jrzwee/PiezoPiano/hardware/pinout/hardware.png

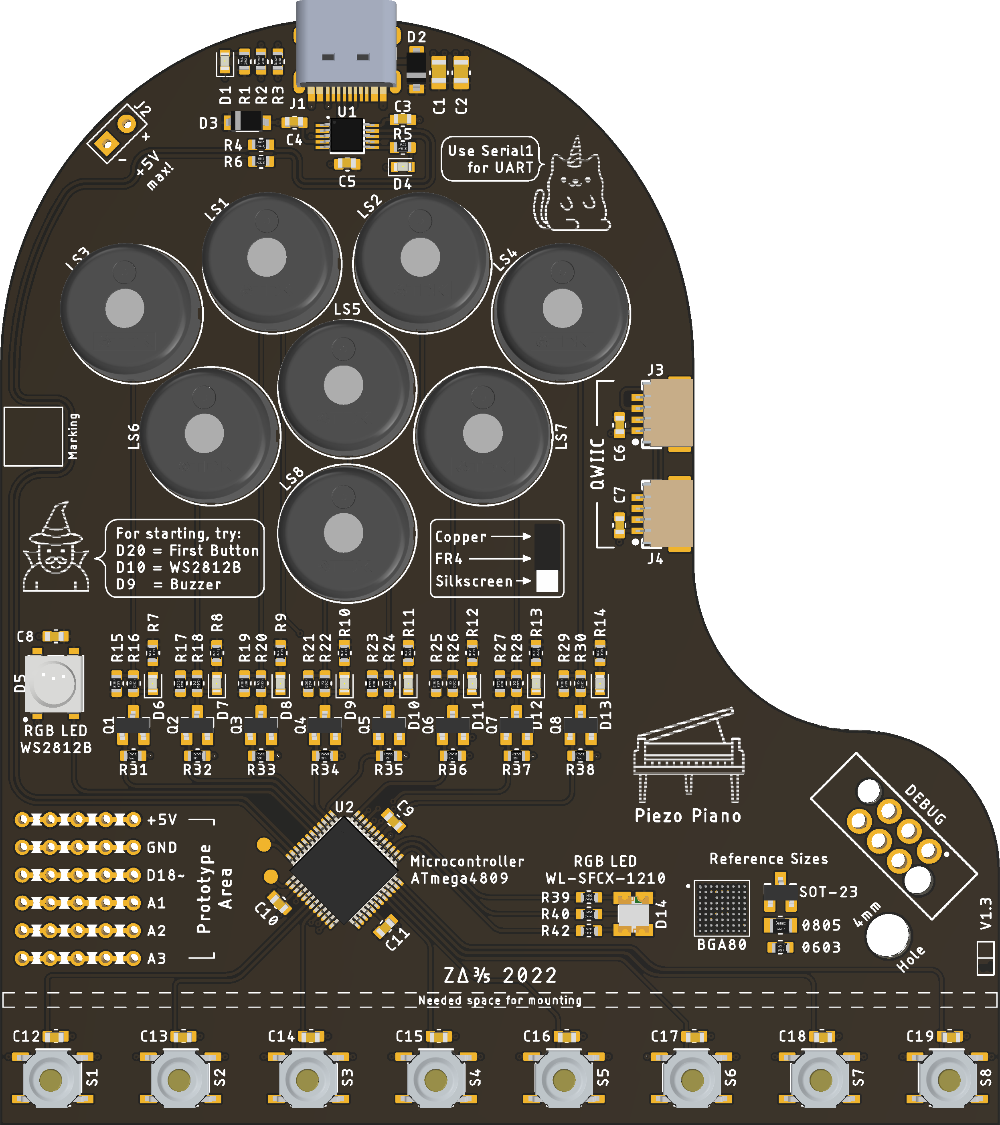
hardware/pinout/hardware.png
