jrzwee/PiezoPiano/hardware/renders/20211024_PiezoPiano_B_V1.2.png

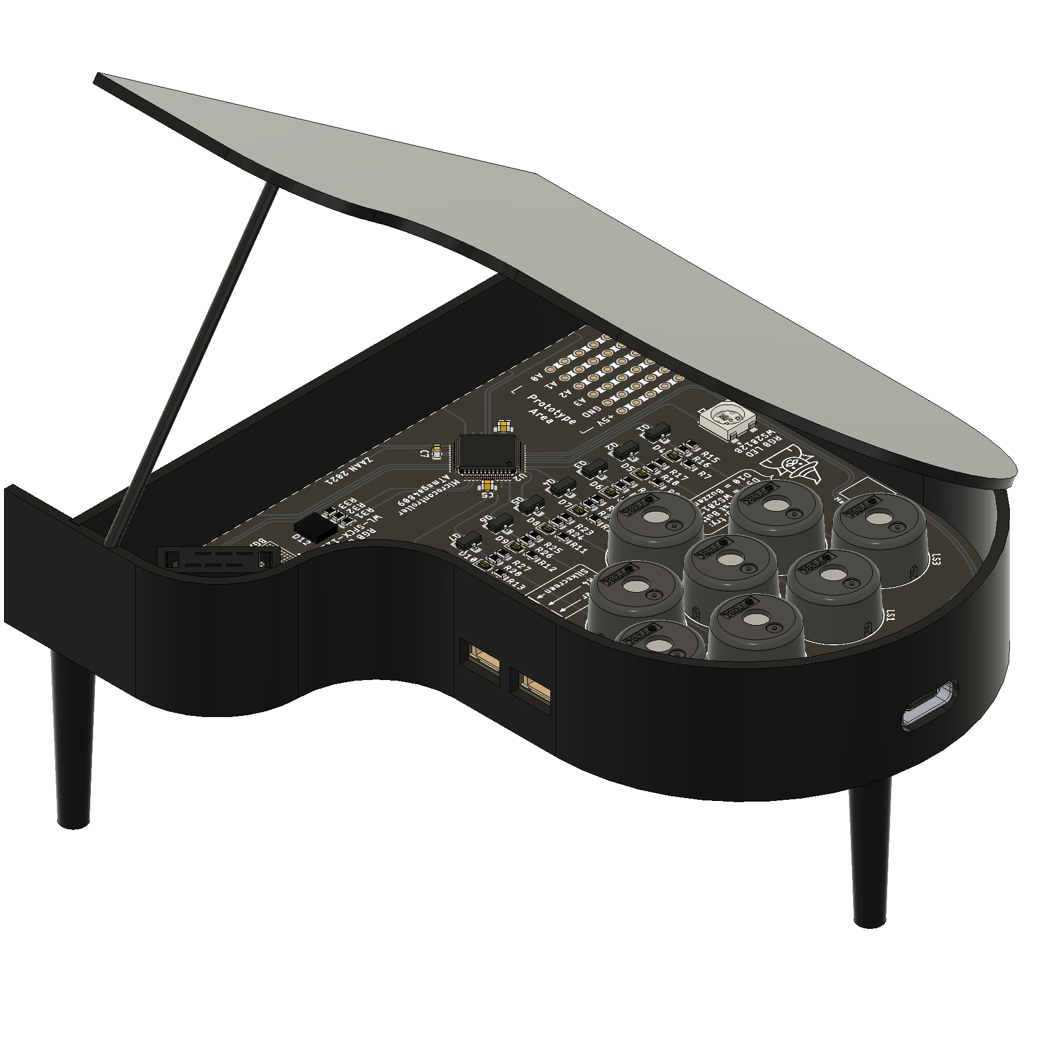
hardware/renders/20211024_PiezoPiano_B_V1.2.png
