jrzwee/PiezoPiano/hardware/renders/piezopiano_b.png

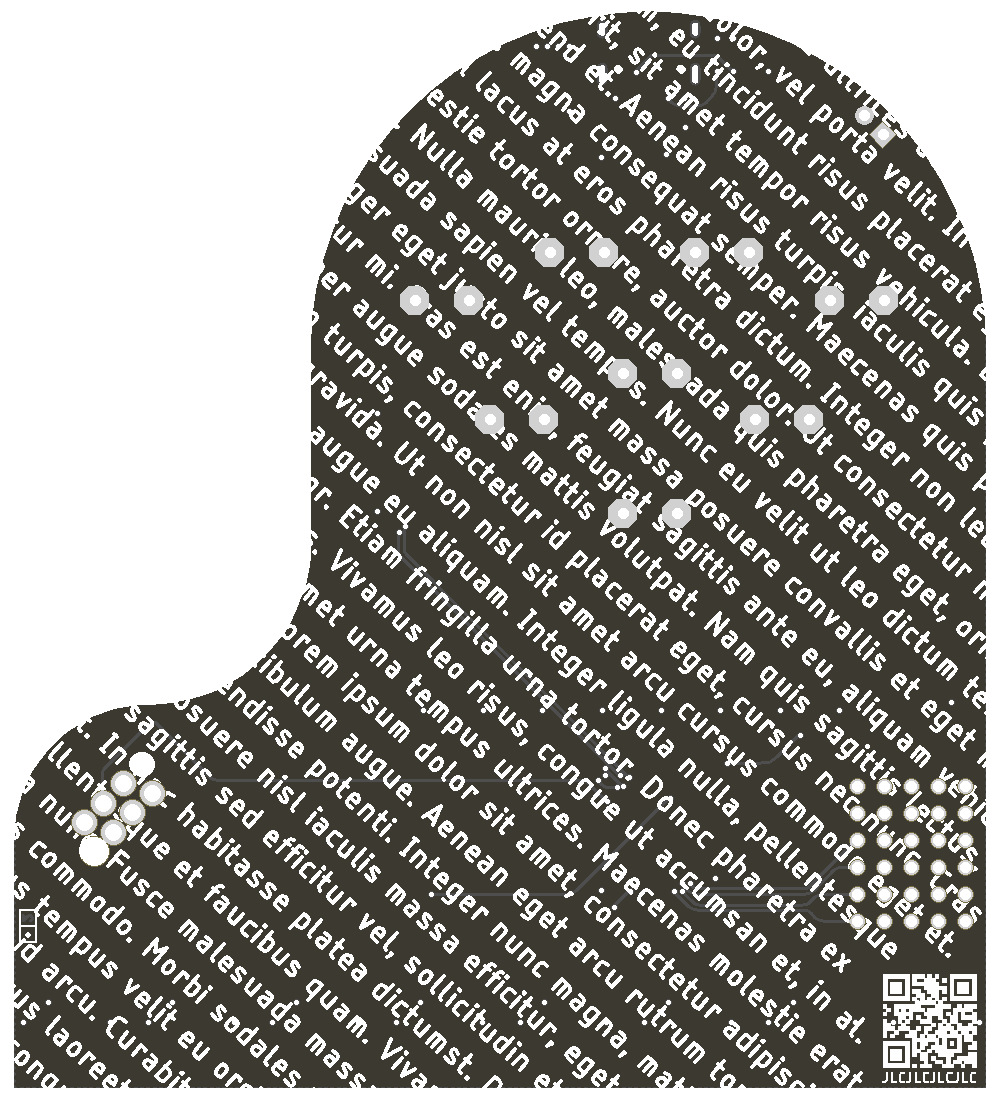
hardware/renders/piezopiano_b.png
