jrzwee/PiezoPiano/hardware/renders/piezopiano_f.png

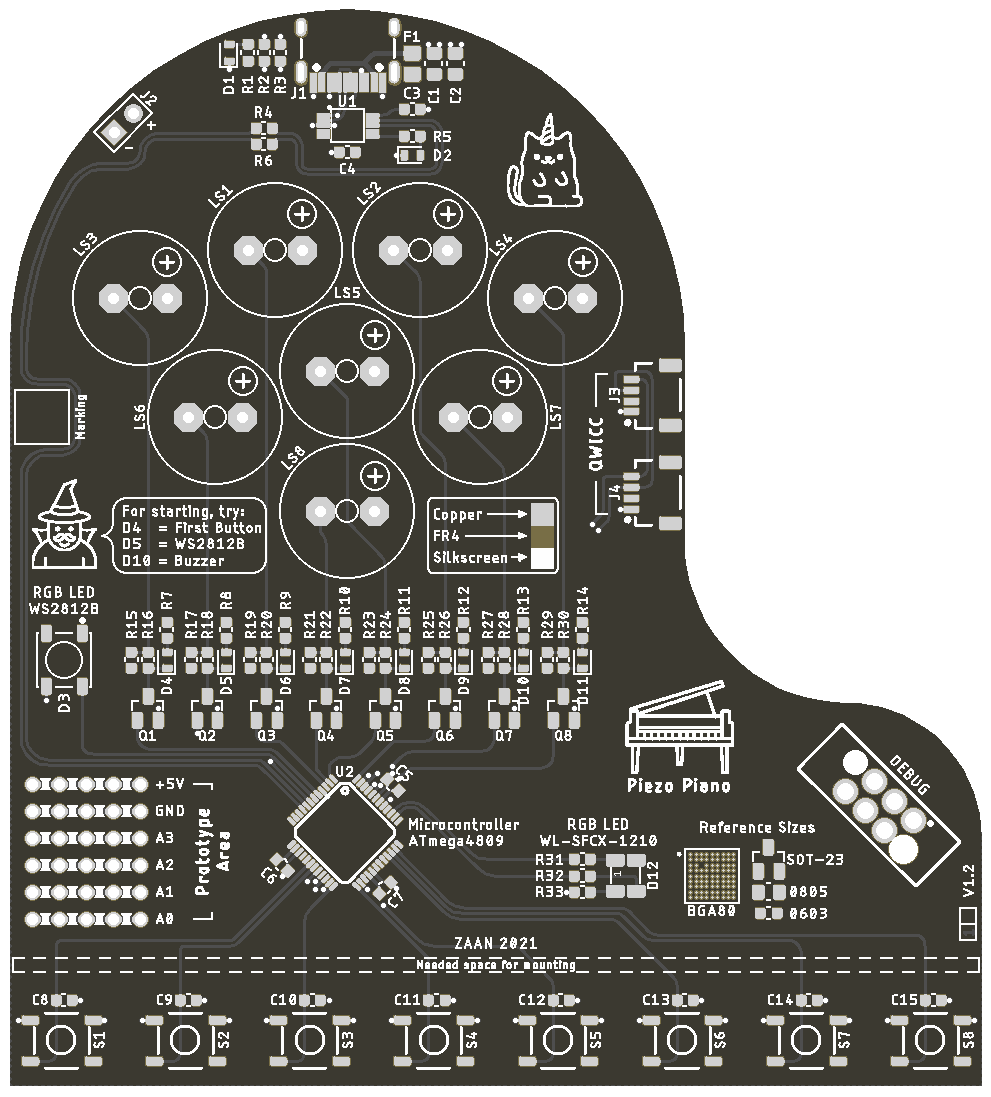
hardware/renders/piezopiano_f.png
