jrzwee/PiezoPiano/firmware/PiezoPiano/HAL/hal_clkctrl.h

/****************************** FH Joanneum ECE16 ******************************

Exercise: 			Bachelor Thesis 1
Date:				2019-01-30
Type:				HAL CLKCTRL (System Clock)

****************************** Andreas Zapfl ******************************/

#ifndef HAL_CLKCTRL_H_
#define HAL_CLKCTRL_H_

// ********************************************* DEFINES ***************
//#define F_CPU 8E6

// ********************************************* PROTOTYPES ***************
void HAL_CLKCTRL_Init();

#endif /* HAL_CLKCTRL_H_ */
