jrzwee/PiezoPiano/firmware/PiezoPiano/HAL/hal_gpio.h

/****************************** FH Joanneum ECE16 ******************************

Exercise: 			Bachelor Thesis 1
Date:				2019-01-30
Type:				HAL GPIO

****************************** Andreas Zapfl ******************************/

#ifndef HAL_GPIO_H_
#define HAL_GPIO_H_

// ********************************************* PROTOTYPES ***************
void HAL_GPIO_Init();


#endif /* HAL_GPIO_H_ */
